hulkco/HexEsp/cp2104/Images/004-female-colors.png

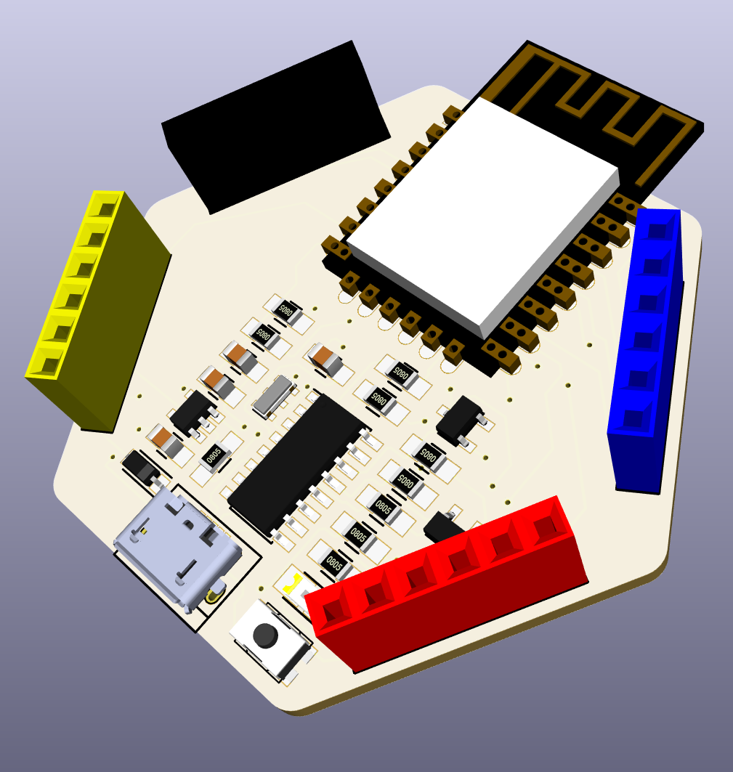
cp2104/Images/004-female-colors.png
