hulkco/HexEsp/ch340/images/2471-14.jpg

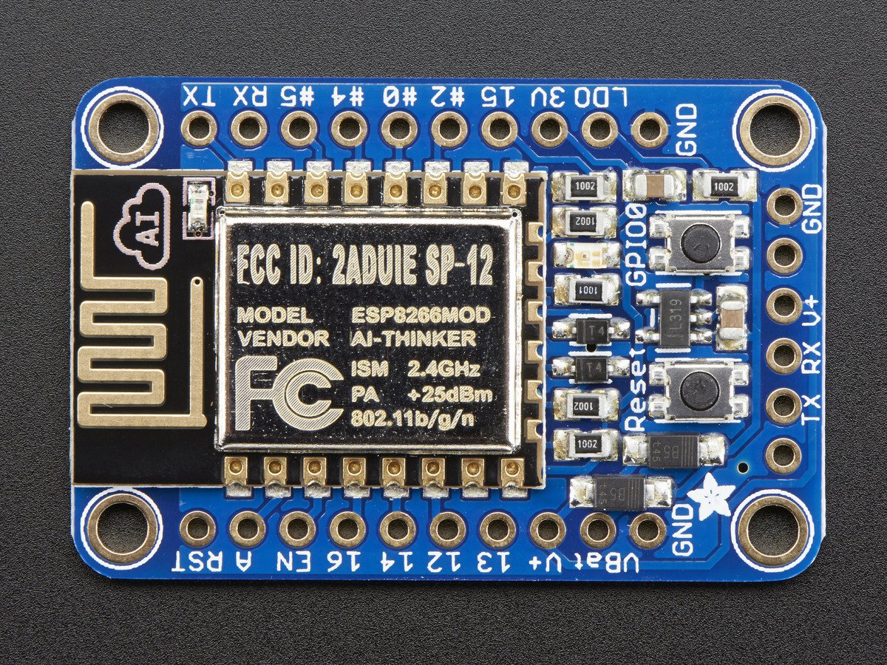
ch340/images/2471-14.jpg
