hulkco/HexEsp/ch340/images/2821-08.jpg

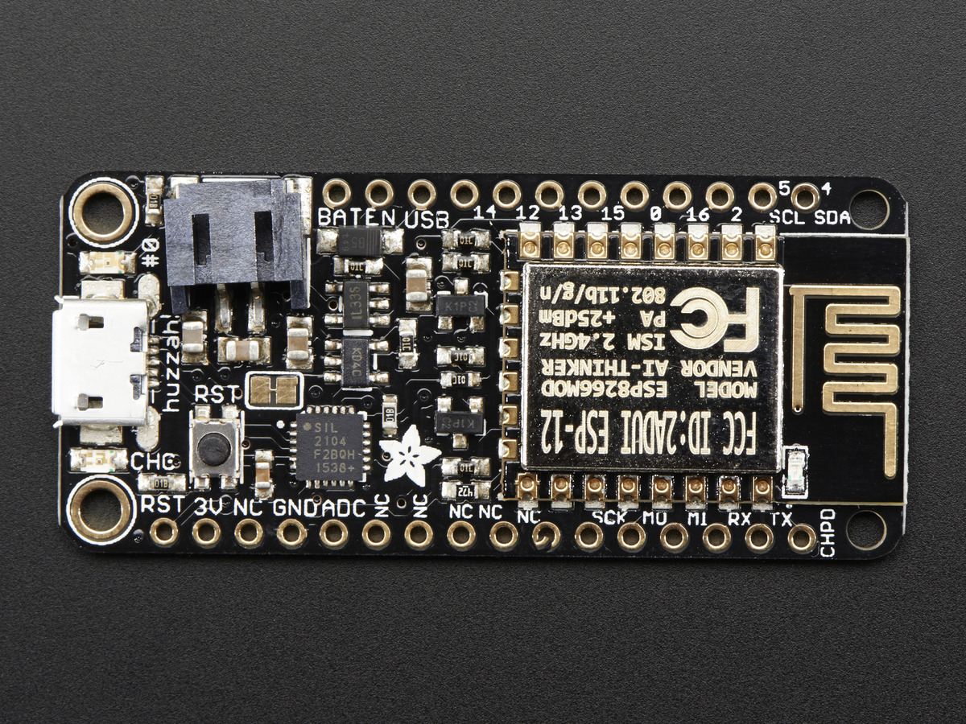
ch340/images/2821-08.jpg
