hulkco/HexEsp/ch340/images/ADA-2821-5-800x533.jpg

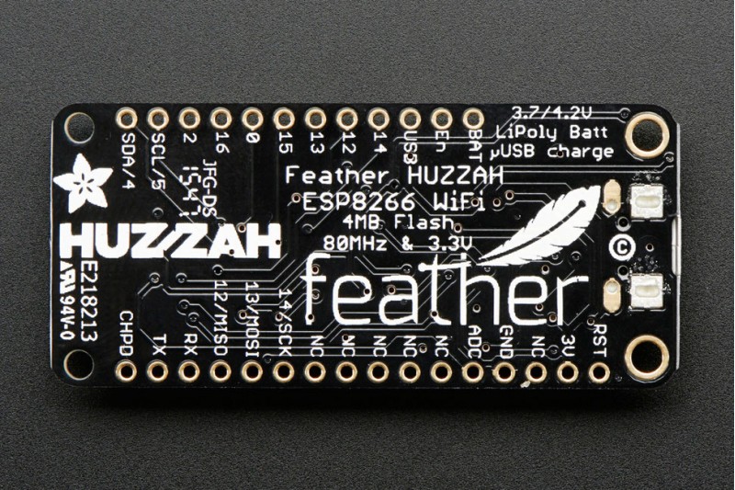
ch340/images/ADA-2821-5-800x533.jpg
