hulkco/HexEsp/ch340/images/Ada_Feather_Tracks.png

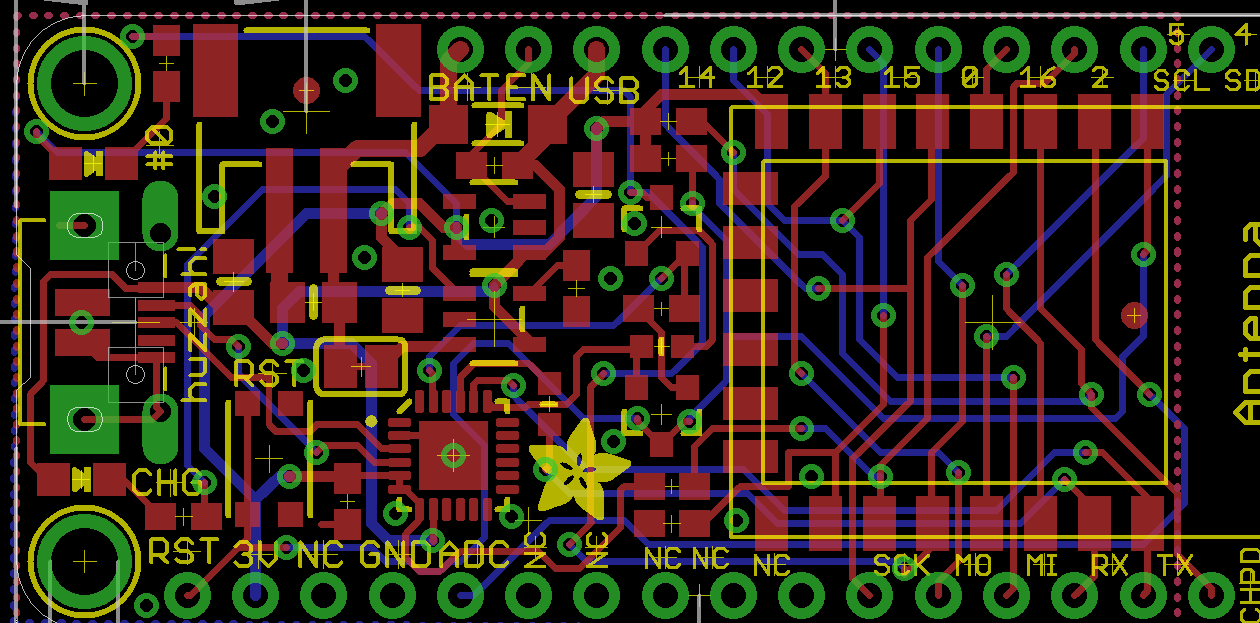
ch340/images/Ada_Feather_Tracks.png
