hulkco/HexEsp/ch340/images/Esquematico_HexEsp.png

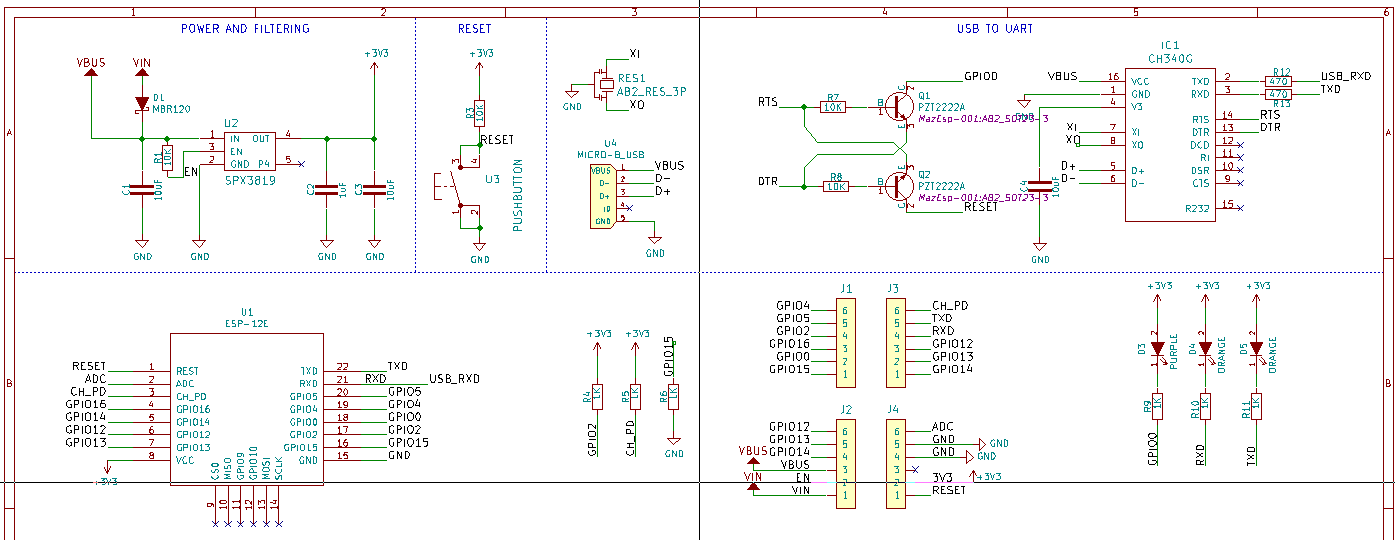
ch340/images/Esquematico_HexEsp.png
