hulkco/HexEsp/ch340/images/HTB1RAMzHpXXXXaxapXXq6xXFXXXq.jpg

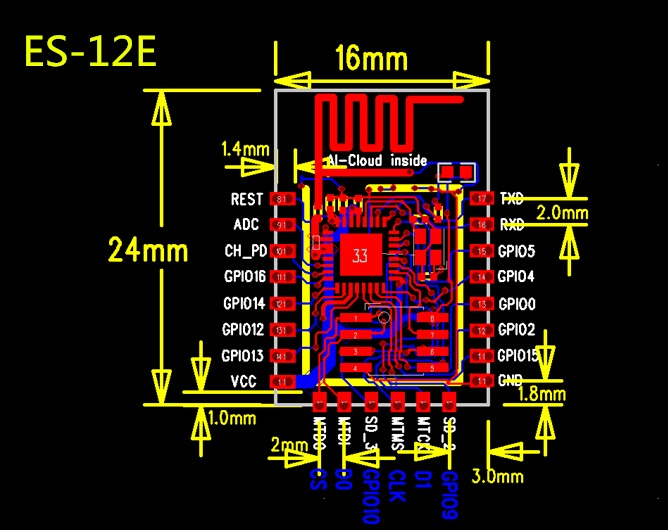
ch340/images/HTB1RAMzHpXXXXaxapXXq6xXFXXXq.jpg
