hulkco/HexEsp/ch340/images/Selección_006.png

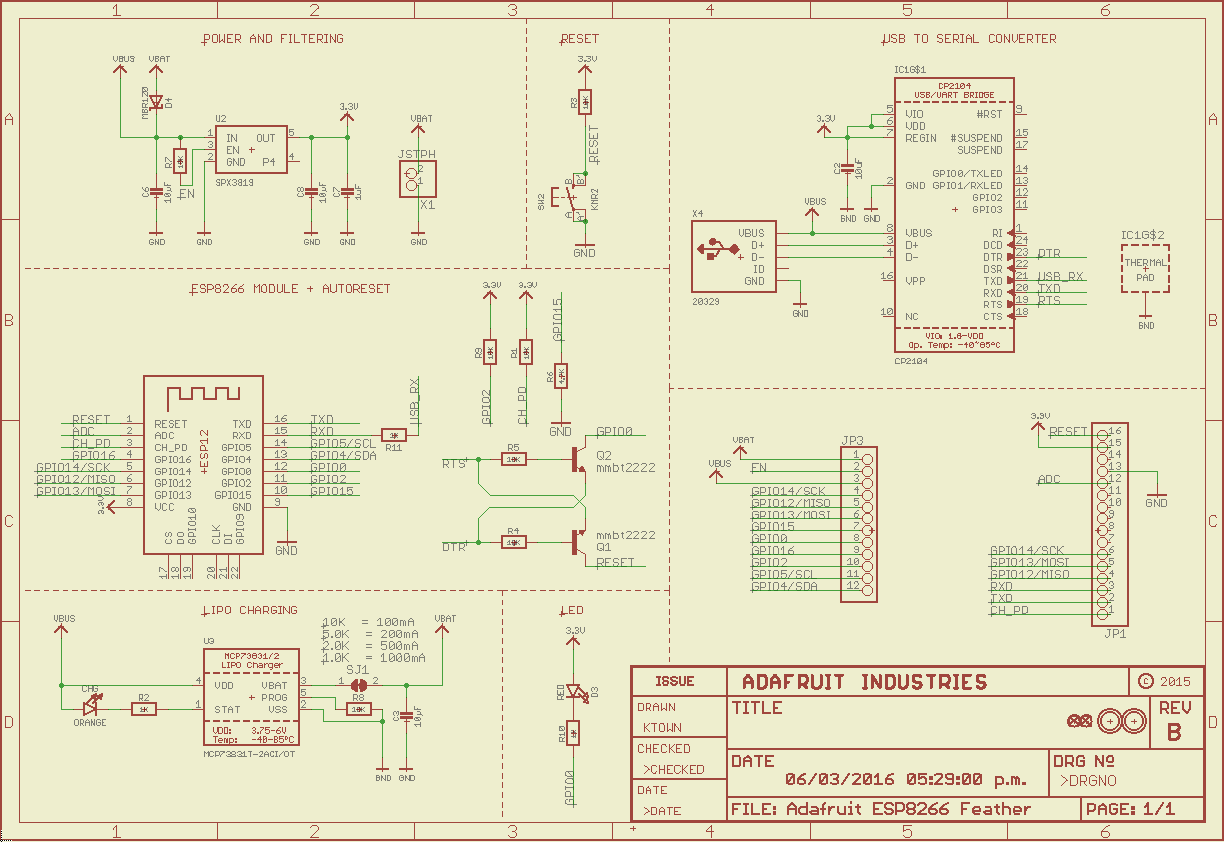
ch340/images/Selección_006.png
