hulkco/HexEsp/ch340/images/Selección_007.png

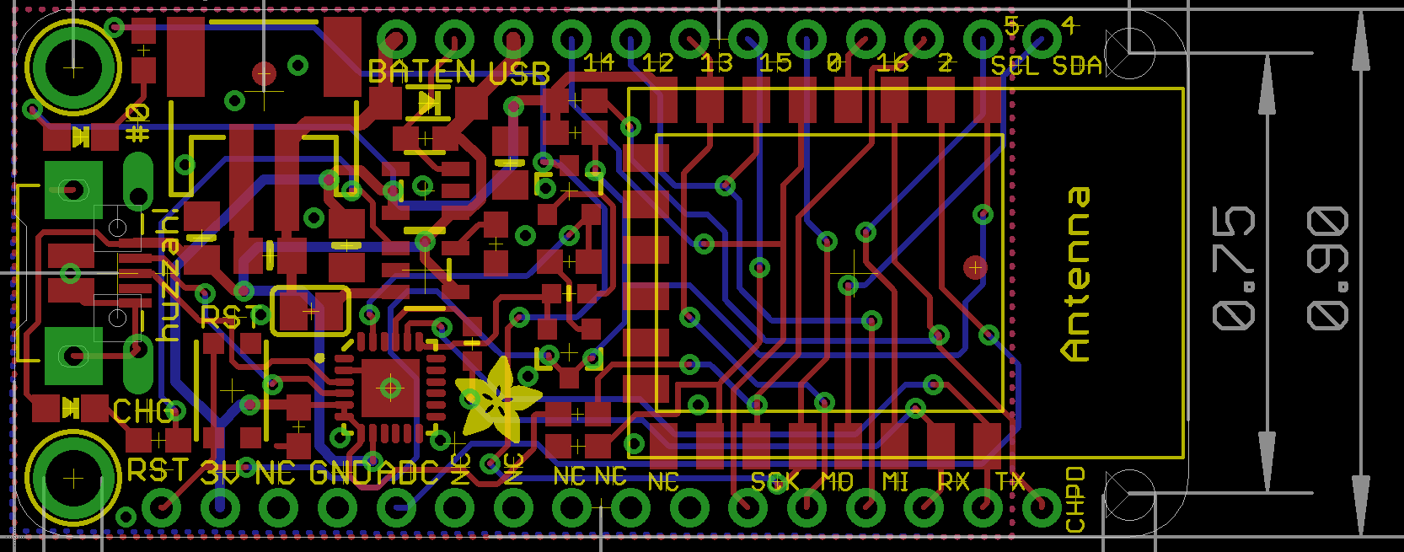
ch340/images/Selección_007.png
