hulkco/HexEsp/ch340/images/SW/50PCs-Micro-TACT-Button-4x4x1.5_SMD.jpg

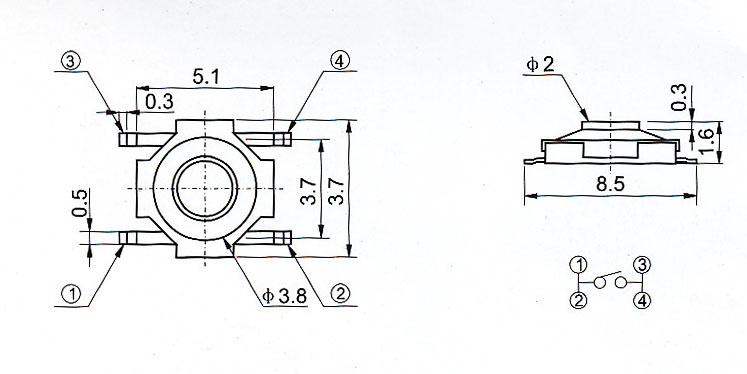
ch340/images/SW/50PCs-Micro-TACT-Button-4x4x1.5_SMD.jpg
