hulkco/HexEsp/ch340/images/SW/2016-08-12 10_45_52-Free shipping 100pcs_lot light touchig Push Button Momentary Tact switch 4x4x1.5.gif

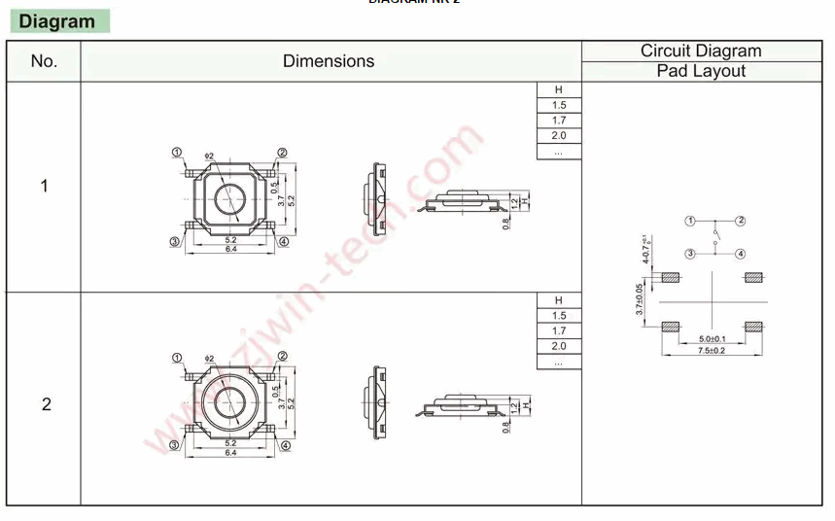
ch340/images/SW/2016-08-12 10_45_52-Free shipping 100pcs_lot light touchig Push Button Momentary Tact switch 4x4x1.5.gif
