hulkco/HexEsp/ch340/pASO/001.png

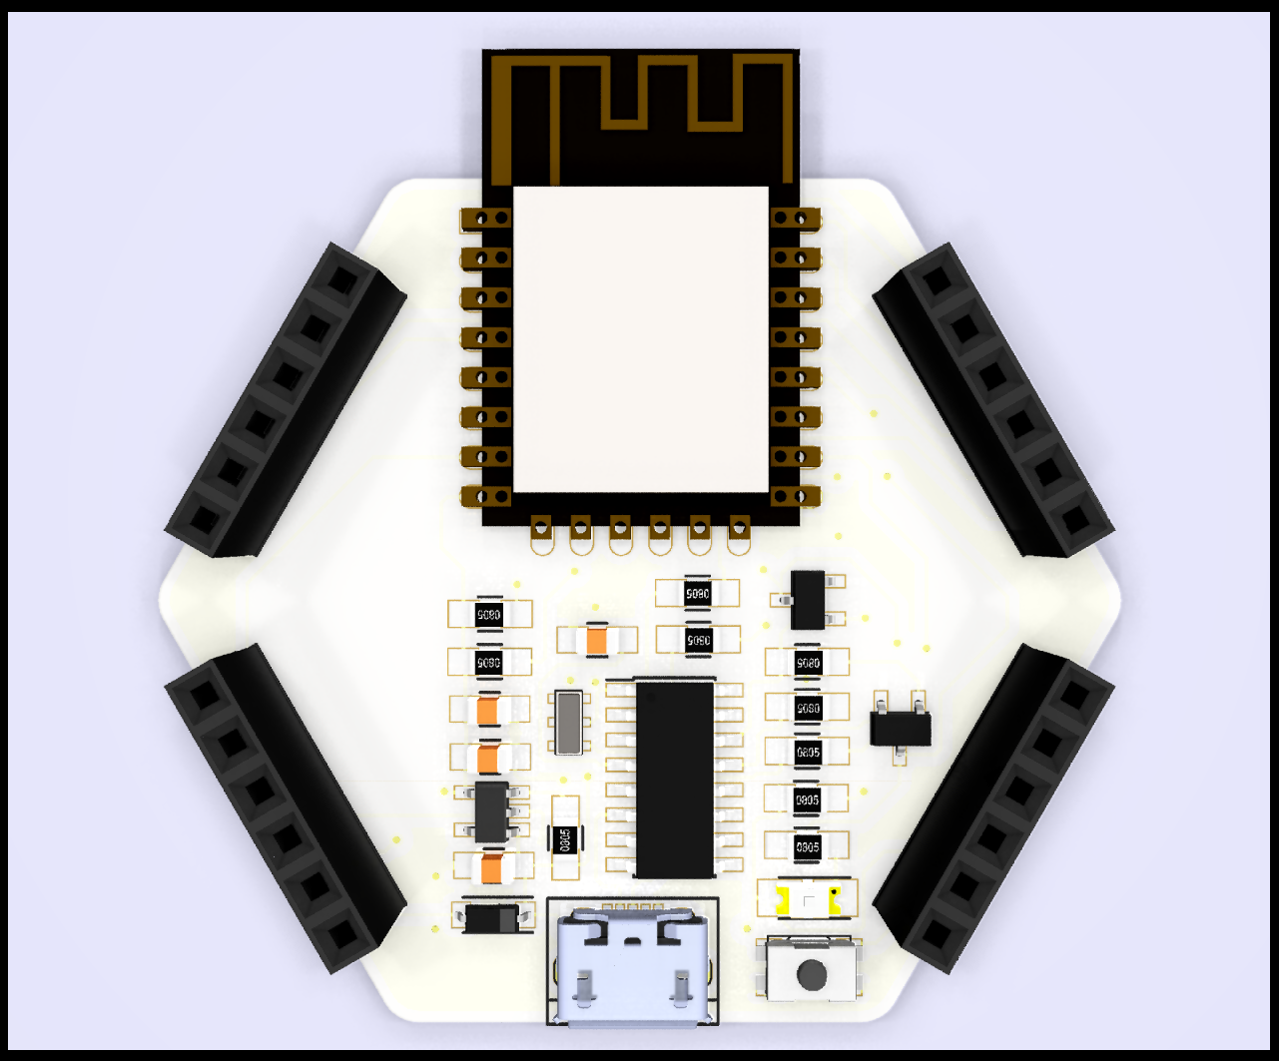
ch340/pASO/001.png
