hulkco/HexEsp/ch340/pASO/002.png

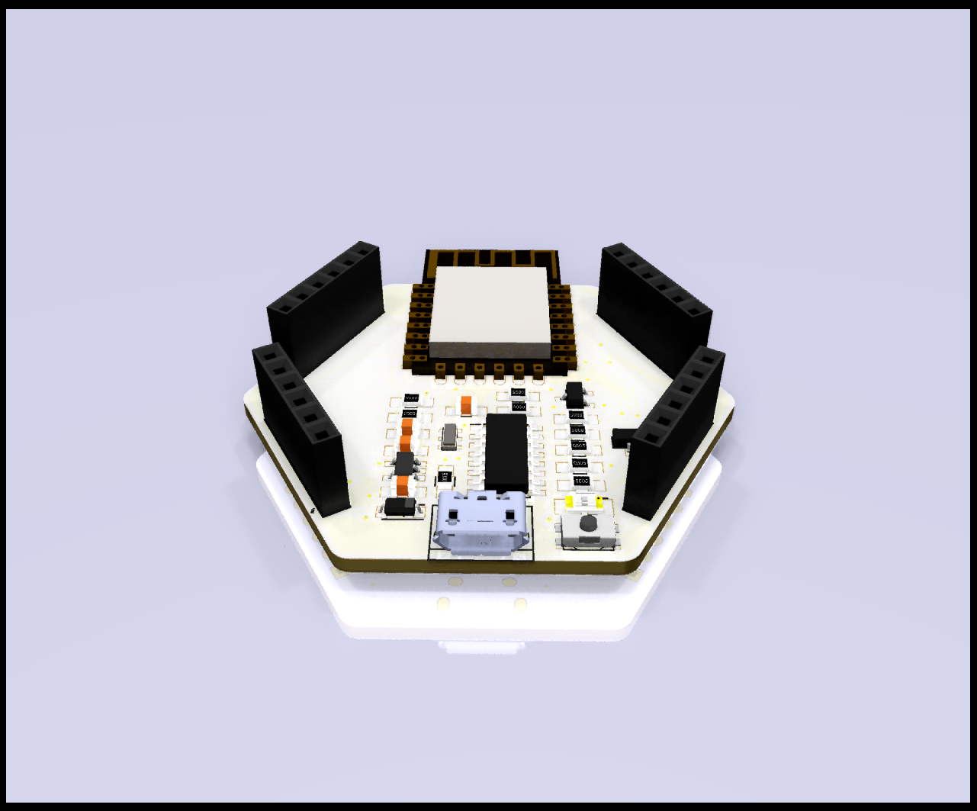
ch340/pASO/002.png
