hulkco/HexEsp/ch340/pASO/003.png

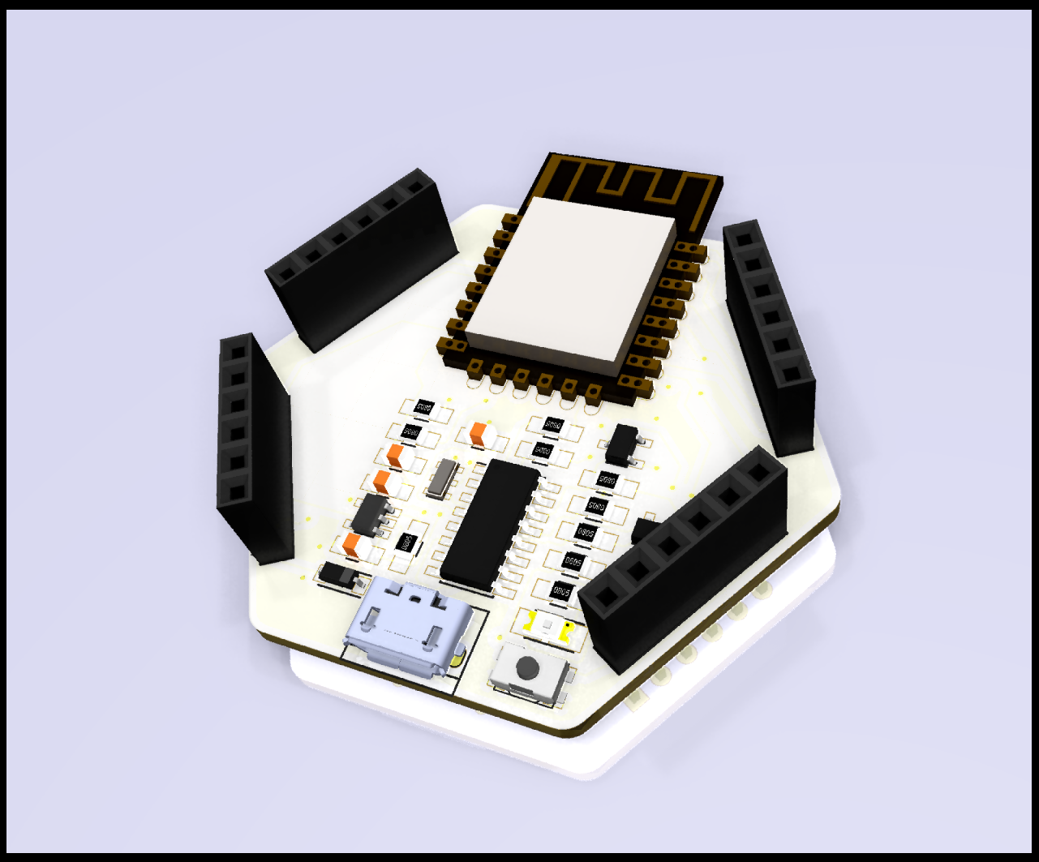
ch340/pASO/003.png
