hulkco/HexEsp/ch340/pASO/005-male-colors.png

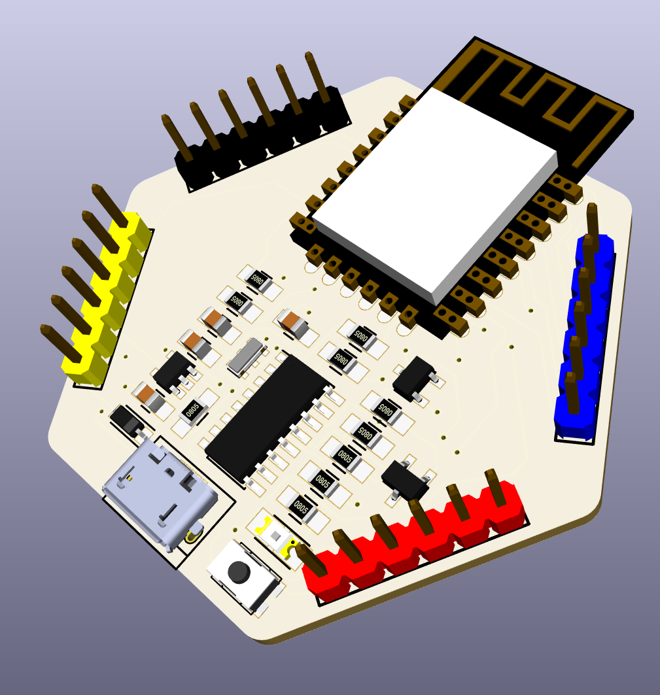
ch340/pASO/005-male-colors.png
