hulkco/HexEsp/cp2104/Docs/ADC_add/2015-07-24T02:34:51.657Z-ESP8266-Analog-Pins-Expander-V2-Breadboard.jpg.2560x2560_q85.jpg

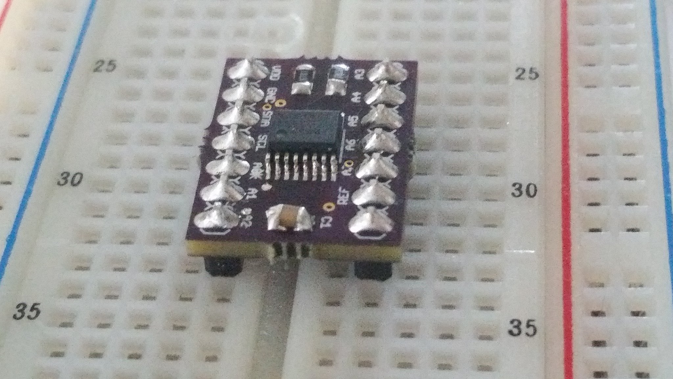
cp2104/Docs/ADC_add/2015-07-24T02:34:51.657Z-ESP8266-Analog-Pins-Expander-V2-Breadboard.jpg.2560x2560_q85.jpg
