hulkco/HexEsp/cp2104/Docs/www/Internet of Home Things » 8 ESP8266 analog inputs for 22 cents_files/graph.jpg

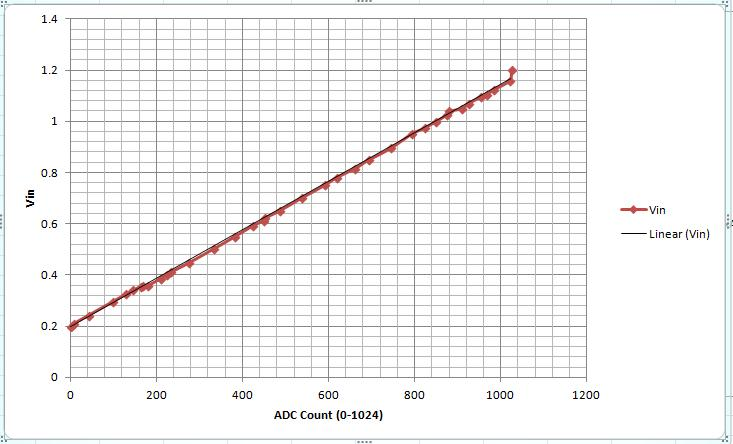
cp2104/Docs/www/Internet of Home Things » 8 ESP8266 analog inputs for 22 cents_files/graph.jpg
