hulkco/HexEsp/cp2104/Docs/www/Internet of Home Things » 8 ESP8266 analog inputs for 22 cents_files/LevelShifter-1024x692.jpg

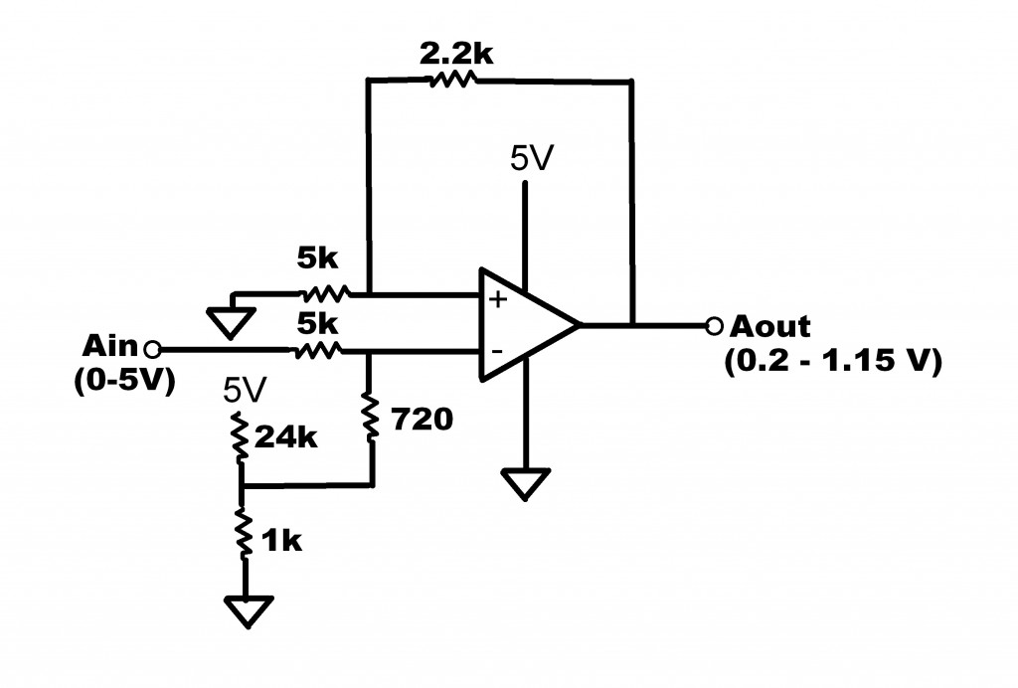
cp2104/Docs/www/Internet of Home Things » 8 ESP8266 analog inputs for 22 cents_files/LevelShifter-1024x692.jpg
