hulkco/HexEsp/cp2104/Docs/www/Internet of Home Things » 8 ESP8266 analog inputs for 22 cents_files/muxpic-150x150.jpg

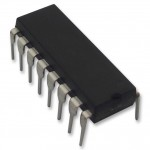
cp2104/Docs/www/Internet of Home Things » 8 ESP8266 analog inputs for 22 cents_files/muxpic-150x150.jpg
