hulkco/HexEsp/cp2104/3D/SMD-RESONATOR.fcstd

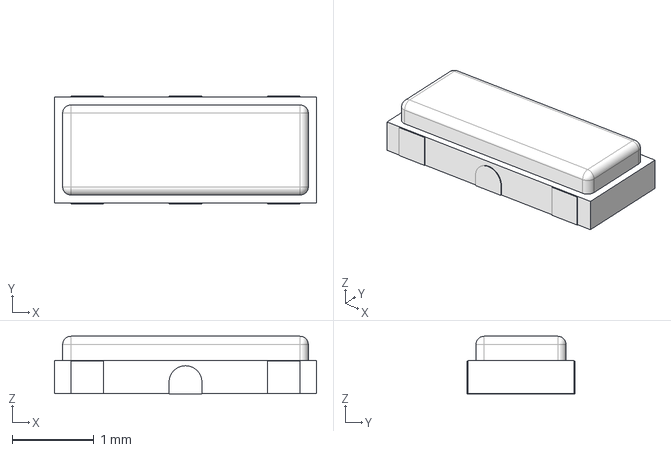
[picture p36: CAD file, 2016-10-04]
cp2104/3D/SMD-RESONATOR.fcstd
3.20 x 1.32 x 0.702 mm
